f3l1xa88077/C2S/Report/Chapters/Intro/Milestones.tex

The project has been divided into five key-phases that each act as sub-projects and each lead into the next. This helps compartmentalise the project for better management and tracking.
\begin{table}[H]
\centering
\begin{tabular}{|l|p{12cm}|}
\hline
\textbf{ID} & \textbf{Milestone} \\
\hline
1 & Design and build a fully custom CubeSat-compatible prototype camera module, including PCB layout, component selection, and sensor integration. \\
\hline
2 & Develop firmware to configure and control the image sensor (e.g., via I\textsuperscript{2}C/SPI), supporting raw image capture and tuning of parameters like exposure, gain, and white balance. \\
\hline
3 & Implement an image pipeline to convert raw sensor data into usable image formats, including demosaicing, gamma correction, and compression. \\
\hline
4 & Design a mechanical housing that meets CubeSat volume, mass, and thermal constraints, and could interface with the rest of the CubeSat. \\
\hline
5 & Test and validate the camera module under simulated space conditions (thermal cycling, vibration, and low light). \\
\hline
\end{tabular}
\caption{Milestone objectives for the duration of the project}
\label{tab:milestones}
\end{table}
