f3l1xa88077/C2S/Report/Chapters/Pre/Summary.tex

This report is a long document, and it is easy to get lost in. The following text aims to help you navigate to the right sections depending on your need. Unfortunately, this project had generated a substantial amount of information, so some key considerations may have been missed or skipped. This report won't teach you everything I know, but \textbf{it will place you in my shoes and teach you why I made my decisions}.
\nl
\autoref{sec:intro} is your extended version of the project proposal. It explores a generic background and rationale for the project. Following this, the project scope is broken down and clearly explained, outlining exactly what is and isn't part of the project. Project milestones illustrate the core outcomes from the project and the responsibilities section shows how each milestone is divided between project members. Lastly, the project timeline presents the expected progression of the project.
\nl
Before diving into the other explanations, it's worth quickly understanding what I'll be referring to when I say v0, v0.1, and v1. It was intended that the project would include two versions, the first being a prototype to confirm functionality (v0), and a flight prototype (v1). Unfortunately, the test board needed to be redesigned, so a revised version of v0 was created, v0.1.
\nl
\autoref{sec:c2sv0} explores the first version of the project's (C2Sv0) hardware that used the MIPI CSI-2 camera interface, which was eventually shelved. This section critically explores each of the core system components and provides thorough justications for each selection. These components mainly map to those used in C2Sv0, but their considerations and justifications are still relevant. You may find that this version is often referred to as the \textit{"breakout board"} or \textit{"P, S, A"} meaning (P)rocessor, (S)ensor, and (A)daptor. The schematic and PCB designs were split into separate sections. This version was deprioritised because the only chips that support the CSI-2 interface have a BGA pitch too fine for manufacturing within current budget limitations. Although this board was not procured, many circuits were recycled for the succeeding version (v0.1) and the content is still worth a read, especially for the CSI-2 interface information.
\nl
\autoref{sec:c2sv0.1} investigates the second version of the project's (C2Sv0.1) hardware which supported the DCMI camera interface. Unlike v0, this interface is older, so the chips that support the interface have much larger packages which were within our manufacturing capabilities. Like v0, the schematics and PCBs are split into different sections. Errors and fixes are mentioned as a remark for each section. \autoref{sec:manufacturing-v0.1} outlines the processes involved in manufacturing and developing the hardware. This involes where the components where sourced from, how the components were placed, as well as the 3D printed designs. \autoref{sec:v0.1-coding} dives into programming the hardware from the previous section. It focuses on coding each individual subsystem first, then tests them all together to confirm compatability.
\nl
The Appendices (\autoref{sec:appendices}) are supplementary materials that are non-essential to the project, but are a useful read. For example, some of the research is included to fill in gaps of knowledge. To the average reader, this is not-critical, but can be insightful.
