f3l1xa88077/C2S/Report/Chapters/v1/Software/Software.tex

These goals were developed from my experiences of what had and hadn't worked with the previous versions, so they may not be perfect, but these are what I found to be the most important steps in camera development. Additionally, it makes writing and, in your case, reading, a lot easier to digest.

% -----------------------
% Setup
% -----------------------
\subsubsection{STM32CubeIDE Setup}

% -----------------------
% Isolated
% -----------------------
\subsubsection{Isolated Testing}

    \subsubsubsection{LEDs}
        \subimport{./Isolated/}{LEDs.tex}

    \subsubsubsection{Button}
        \subimport{./Isolated/}{Button.tex}

    \subsubsubsection{CSA}
        \subimport{./Isolated/}{CSA.tex}

    \subsubsubsection{QSPI}
        \subimport{./Isolated/}{QSPI.tex}

    \subsubsubsection{Sleep}
        \subimport{./Isolated/}{Sleep.tex}

    \subsubsubsection{RTOS}
        \subimport{./Isolated/}{RTOS.tex}

    \subsubsubsection{USB}
        \subimport{./Isolated/}{USB.tex}

    \subsubsubsection{Camera}
        \subimport{./Isolated/}{Camera.tex}

    \subsubsubsection{microSD}
        \subimport{./Isolated/}{microSD.tex}
