f3l1xa88077/C2S/Report/Chapters/Appendices/Supporting Calculations/Stitching.tex

For a given frequency, the center-to-center pitch between the vias should be less than approximately:
\begin{equation}
    L < \frac{c}{8f\sqrt{Dk}}
\end{equation}
