f3l1xa88077/C2S/Report/Chapters/Appendices/Supporting Calculations/Supporting Calculations.tex

\subsection{C-L-C Values}\label{sec:clc-values}
    \subimport{./}{CLC.tex}

% \subsection{Transconductance of Oscillator}
%     \subimport{./}{Transconductance.tex}

% \subsection{Power Draw Estimation}\label{sec:power-draw}
%     \subimport{./}{Power Estimation.tex}

\subsection{Stitching Via Calculations}\label{sec:stitching-calc}
    \subimport{./}{Stitching.tex}
