f3l1xa88077/C2S/Report/Chapters/v1/Planning/Trade.tex

A trade study is a structured evaluation used to identify the most balanced technical solution from a set of alternatives. This helps identify critical system indicators like interface standards and memory type that are vital for developing strong system requirements.

\subsubsubsection{CIS}
    \subimport{./Trade/}{Sensor.tex}

\subsubsubsection{OBC Interface}
    \subimport{./Trade/}{OBC.tex}

\subsubsubsection{CSA}\label{sec:v1-trade-csa}
    \subimport{./Trade/}{CSA.tex}

\subsubsubsection{Memory}\label{sec:v1-trade-memory}
    \subimport{./Trade/}{Memory.tex}

\subsubsubsection{MCU}
    \subimport{./Trade/}{MCU.tex}

\subsubsubsection{Power}
    \subimport{./Trade/}{Power.tex}
