f3l1xa88077/C2S/Report/Chapters/v1/Hardware/Schematic/Clocks.tex

I was able to recycle the same clocks from \autoref{sec:v0.1-clocks} since the x and the x had the same frequency requirements.

\begin{itemize}
    \item \href{https://www.mouser.com/ProductDetail/ECS/ECS-TXO-2016-33-400-TR?qs=PzGy0jfpSMtctR53CPxRHg%3D%3D}{40 MHz TCXO Oscillator (MCU)}
    \item \href{https://www.mouser.com/ProductDetail/ECS/ECS-327TXO-2012-33-TR?qs=amGC7iS6iy%252Bnhf6zW2Y7hQ%3D%3D}{32.768 kHz TCXO Oscillator (MCU)}
\end{itemize}

Since all three oscillators are TCXO, they already include internal circuitry (like the capacitor configuration) and simply need to be connected to the input pins of the STM32.
Each oscillator should continuously produce a clock signal when its tri-state function is enabled. The tri-state pins are tied to VDD so the clocks are always enabled, allowing the MCU to use HSE and LSE during sleep.
\nl
Future versions of the project could connect to the tri-state to the OBC CS line via a NOT gate, which allows the clocks to be externally controlled by the OBC, or continuously run. This switch would allow the OBC to place the clocks into low power mode, and keep the clocks always running during programming when power consumption is not an issue. Then the MCU could switch between its internal and external clocks between sleep modes to save power. This is a complicated approach and was not a requirement for the current verison, so it was not implemented.

\paragraph{Remark}
As the Real Time Clock (RTC) is not used, it was not necessary to include an LSE.
