f3l1xa88077/C2S/Report/Chapters/v1/Hardware/Schematic/Connectors.tex

Camera connector according to \autoref{sec:v1-schematic-sensor}.
\nl
As mentioned in \autoref{sec:v1-schematic-mcu}, a protective resistor was placed in series with the master selector header. OBC 16-pin FFC/FPC connector was reversed to ensure proper connection.
\nl
Please see \autoref{sec:v1-schematic-stlink} for more regarding the STLINK/V2 connector.
\nl
The microSD breakout header pinout developed according to the \href{https://core-electronics.com.au/attachments/localcontent/microSD-Breakout-v14_8139a6ca52.pdf}{BOB-00544 schematic}. Orientation did not matter since the header could be rotated 180° on the PCB.

\paragraph{Remark}
After the PCB was developed and manufactured, the 16-pin FPC pinout on OBC was reversed, so a reverse cable is required otherwise a short-circuit will occur.
\textbf{It is imperative that a reverse cable is used}.
