f3l1xa88077/C2S/Report/Chapters/v1/Software/Isolated/Button.tex

The button was configured as an external interrupt pin, triggering on the rising edge. Inside the interrupt file, the pin is checked and then sets a flag to capture an image.
