f3l1xa88077/C2S/Report/Chapters/v1/Software/Isolated/LEDs.tex

The LEDs were configured as GPIO outputs, driving HIGH to turn on the LEDs.
