f3l1xa88077/C2S/Report/Chapters/v1/Software/Isolated/microSD.tex

As outlined in \autoref{sec:v1-microSD}, the SPI interface was not configured correctly, so it was not possible to write/read to the microSD card. I did try adapting SPI libraries and bit-banging with a GPIO pin, but I had no luck.
