f3l1xa88077/C2S/Report/Chapters/v1/Software/Isolated/QSPI.tex

The QSPI driver was carried over from v0.1.
