f3l1xa88077/C2S/Report/Chapters/v1/Hardware/Schematic/Power.tex

The power circuit is responsible for sinking current and delivering stable voltages to the rest of the board. There are five clearly defined sections in the power delivery schematic.

\paragraph{1a. USB-C Connection}
A USB-C connector uses 5.1 k$\Omega$ pull down resistors (as outlined on page 54 of \cite{ti-usb-typec-guide}) to convert the load to a sink. The connector outputs +VUSB, which should be roughly 5V according to \cite{ti-usb-typec-guide}. The communication pins have been left as NC since the STLINK already provides a virtual COM port.

\paragraph{1b. EPS Connection}
Sinks a stable 5V from the EPS board, named +VEPS.

\paragraph{2. Source Selection}
A three pin header allows the power source to be selected by shorting the middle pin with either the USB or EPS voltage. The output is +VSEL (Voltage Selected).

\paragraph{3. Power Measurement}
+VSHUNT is passed through a shunt resistor, where the voltage difference is recorded by an INA219 CSA (as selected in \autoref{sec:v1-trade-csa}). 
With both address pins of the INA219 tied to ground, its address becomes 0x40, which does not clash with the read and write addresses of the OV7670 (0x42 and 0x43).
The CSA outputs current, voltage, and power data via I2C. The terminating side of the shunt resistor has +VCSA.
The selected LDO has a maximum output current of 300 mA on 3V3 logic which sinks 200 mA at 5V.
I selected the shunt resistor value according to the maximum voltage range (gain /8) of the INA219, this meant if less current was being drawn, the gain could be changed for increased accuracy i.e., worst case scenario the gain is /8 and I can characterise at max current draw, or during power-efficient modes where the current draw is low, I could change the range to $\pm$80 mV or $\pm$ 40 mV for better accuracy.
To achieve a 320 mV swing at 200 mA, a 1.6 $\Omega$ shunt resistor, the \href{https://au.mouser.com/ProductDetail/Panasonic/ERJ-6DQF1R6V?qs=WO7YBshssFHHp%2FMEk%2F2ARA%3D%3D}{ERJ-6DQF1R6V} was selected.
The 0805 package was selected to make the shunt more identifiable, although the 0603 package was perfectly fine to use.
The shunt resistor will dissipate some power, 64 mW at its peak, but we know its resistance and the current going through, so we can subtract its dissipated power from the total power to identify how much power only the board is consuming.

\paragraph{4. Filtering}
+VCSA is then passed through a pi-filter (CLC network) to reject any high-frequency noise, with output +VFILT (Voltage Filtered). I chose capacitor values of $C_1=$100 nF and $C_2=$10 $\mu$F (\autoref{sec:clc-values}) to create a cut-off frequency $\approx$1 MHz.

\paragraph{5. 3V3 Regulation}
Lastly, +VFILT is regulated to +3V3 using a Low-Dropout (LDO) regulator, specifically, the \href{https://au.mouser.com/ProductDetail/Texas-Instruments/TPS7A2033PDBVR?qs=hd1VzrDQEGjk%2FOBnRfKB4A%3D%3D}{TPS7A2033PDBVR}. This component was selected because of its high Power Supply Rejection Ratio (PSRR), its ability to provide a low-noise DC output for sensitive analog components, and its minimal PCB footprint due to the lack of an external inductor (see \autoref{sec:v1-sensor-power} for more about the specifics of PSRR). The datasheet was followed to populate the schematic.
