f3l1xa88077/C2S/Report/Chapters/v1/Hardware/PCB/Power Pad.tex

The same design considerations from version 0.1 were used, please see \autoref{sec:v0.1-powerpad} for more.
