f3l1xa88077/C2S/Report/Chapters/v1/Hardware/Schematic/Button.tex

Unlike for Version 0.1 in \autoref{sec:v0.1-sch-other}, only one button was used as the NRST pin was connected to the STLINK/V2 and BOOT0 could be left inactive according to \href{https://community.st.com/t5/stm32-mcus-boards-and-hardware/confused-over-correct-connections-for-boot0-nrst-and-swd/td-p/61611}{this article}. In addition, the \href{https://au.mouser.com/c/electromechanical/switches/tactile-switches/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}{PTS636} was used as it was the smallest and cheapest button that appeared in the Mouser search for tactile ON-OFF SMD/SMT switches. Keeping the button size small helped making space for more larger and more space-critical components like the connectors. The 2-pin symbol also made it impossible to short VCC and GND on the pinout.
