f3l1xa88077/C2S/Report/Chapters/v0/Intro/Introduction.tex

This phase focuses on establishing the foundation for the project by defining system requirements, selecting the image sensor, planning the preliminary architecture, and conducting initial parts research.
\nl
\textit{Please note. Although certain components are investigated, I only focus on key-components like the sensor and processor. Resistors, capacitors, debug LEDs and other components mentioned in dataSchematic (like recommended circuits) are not discussed. For more information, please see \autoref{sec:v0-schematic}}
