f3l1xa88077/C2S/Report/Chapters/v0/Schematic/Overview.tex

This phase involves designing the camera circuit schematic using Altium Designer, laying the groundwork for subsequent PCB development and component selection.
\nl
The schematic is divided into eight sub-sheets:
\begin{enumerate}[noitemsep]
    \item Processor
    \item Image Sensor
    \item Clocks
    \item uSD Card
    \item LPS
    \item SWD Connector
    \item USBC Connector
    \item Power Sequencer
\end{enumerate}
