f3l1xa88077/C2S/Report/Chapters/v0/Schematic/SWD.tex

The SWD connector followed the \href{https://www.youtube.com/watch?v=PMEpQZ90f34}{Phil's Lab guide} on STM32 PCB design, as well as referencing the ADCS Integration Board for the component.
