f3l1xa88077/C2S/Report/Chapters/v0/Schematic/uSD.tex

I used the getting started guide to construct the uSD Card schematic. Like the guide, I used the \href{https://au.mouser.com/ProductDetail/Nexperia/NXS0506GUX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}{NXS0506GUX} since the recommended component uses a BGA package that is too fine.
\nl
For faster readout speeds, I have connected the component in 4-bit mode, opposed to the simpler, but slower, 1-bit mode (connecting only DAT0).
\nl
Additionally, I added a decoupling capacitor to VCC using same value as the decoupling capacitors used on the image sensor.
