f3l1xa88077/C2S/Report/Chapters/v0.1/Programming/Isolated/Isolated.tex

\subsubsubsection{LEDs}
\subimport{./}{LEDs.tex}

\subsubsubsection{Audio Buzzer}\label{sec:buzzer}
\subimport{./}{Buzzer.tex}

\subsubsubsection{Rotary Encoder}
\subimport{./}{Encoder.tex}

\subsubsubsection{Current Sense Amplifier}\label{sec:csa}
\subimport{./}{CSA.tex}

\subsubsubsection{OR Gate}
\subimport{./}{OR.tex}

\subsubsubsection{Buttons}
\subimport{./}{Buttons.tex}

\subsubsubsection{QSPI}
\subimport{./}{QSPI.tex}

\subsubsubsection{microSD}
\subimport{./}{uSD.tex}

\subsubsubsection{Image Sensor}
\subimport{./}{Sensor.tex}
