f3l1xa88077/C2S/Report/Chapters/v0.1/Programming/Isolated/QSPI.tex

Because there were no publicly available drivers for the \href{https://www.renesas.com/en/products/at25sf2561c/part-details/at25sf2561c-mwub-t}{AT25SF2561C} QSPI memory, I developed a custom driver to interface with our hardware. While STM32CubeIDE provides the underlying HAL functions to support the QSPI interface, the driver logic had to be built from scratch by following the device \href{https://www.renesas.com/en/document/dst/at25sf2561cat25qf2561c-datasheet?r=25559121}{datasheet}.
\nl
The HAL functions operate on \verb|sCommand|, a struct that tells the HAL everything it needs to know like the address, the amount of bytes, how many lines the instruction will be sent on, etc. At its core, my driver simply grabs all the information it needs to, packages it into this \verb|sCommand| struct and feeds that to the HAL to handle the read/write.
Naturally the driver is more complex than this, but if you analyse the code, you will see lots of lines like \verb|QSPI_Memory->sCommand->...| which are just packing the data into the struct.
\nl
Now, by analysing the command set and register maps, I identified four primary operations required for the driver:
\begin{enumerate}[label=(\roman*)]
    \item Writing a byte to a specific configuration or status register.
    \item Reading a byte from a register to monitor device status.
    \item Sending standalone opcodes/commands for state control.
    \item Executing memory erase operations (sector or block level).
\end{enumerate}
Every other high-level function in the driver is essentially a combination of these four primitives.

Before the chip can handle standard read, write, or erase tasks, a specific initialisation sequence is required:
\begin{itemize}
    \item Setting the Write Enable Latch in Status Register (SR) 1.
    \item Validating the Ready/Busy bit in SR1 to ensure the chip isn't mid-operation.
    \item Enabling 4-line data transfer in SR2.
    \item Configuring latency in SR3 to match our clock frequency.
    \item Entering 4-byte address mode to access the full memory capacity beyond $16$\,MB.
\end{itemize}

A technical constraint of the hardware is that the standard write command is limited to a single $256$-byte page. To handle larger data writes, the driver segments the data into $256$-byte chunks and automatically increments the address pointer to the next page once the current one is full. This allows for contiguous data writing without manual page management.
\nl
Beyond the basic command set, several hardware-level constraints were addressed to ensure data integrity:
\begin{itemize}
    \item While the device supports 256-byte page programming, memory must be cleared in 4\,kB sectors before a rewrite can occur. The driver includes safety checks to prevent writing to non-erased blocks.
    \item The 4-byte address mode and dummy cycle configurations are volatile; the driver re-initialises these parameters on every power-on reset to ensure the memory map is consistently accessible.
    \item All polling loops for the RDY/BSY bit incorporate defined timeout periods to prevent CPU hang-ups in the event of hardware communication failure.
\end{itemize}

To simplify the integration of the driver into the flight software, I had created a \verb|DataBlock| structure to manage data transfers. This structure bundles the data size, source/destination pointers, and memory addresses into a single object, helping to abstract and simplify the code.
\nl
The driver's internal address management automatically updates its tracker. This ensures that subsequent write calls will append data to the next available 4\,kB-aligned sector, preventing data overwrites.
\nl
The driver utilises a LIFO (Last-In, First-Out) stack architecture for memory management, so new data chunks are pushed onto the next available address. Erase operations are designed to pop the most recent data by moving the address tracker backward. Because the address tracker is a single scalar value, erasure must occur in reverse-chronological order. Erasing a chunk at the start or middle of the memory would cause the tracker to point toward valid data further up the stack, leading to addressing conflicts.
\nl
Although the data chunks could be managed with a data structure, the symptoms of implementing a structure introduces far more complex problems than positive benefits. For example, two image chunks $I_1$ and $I_2$ with two characteristic sizes cannot be stored side by side without wastage. If $I_1$ is stored directly before $I_2$ in memory, then $I_1$ cannot be deleted and replaced with a chunk of different size without overwriting $I_2$ of leaving empty space between the chunks. For these reasons, implementing data structures is not within the current scope. Instead careful usage of the driver is urged.
