f3l1xa88077/C2S/Report/Chapters/v0.1/Programming/Isolated/uSD.tex

Since the U5 can do internal pull-ups on the data lines with ESD protection, the resistors could have been omitted from this version as mentioned by \href{https://www.youtube.com/watch?v=aEwwQMdKd-c\&t=248s}{Phil's Lab} \cite{phils-lab-sd}. Although, as mentioned in the video, it is recommended to include the resistors for the final build \cite{phils-lab-sd}.
\nl
FileX was used to write and read data to the microSD card. A stream data function was generated to allow larger files to be written, like image data.
