f3l1xa88077/C2S/Report/Chapters/v0.1/Hardware/PCB/Fiducial.tex

Fiducial markers were added to the sensor board (labelled "FM"). Three global markers were added near the corners of the board, and one local marker was added next to pin 1 of the BGA.
Although a pick and place machine is not used, it may help AT\&MWA when they attempt to place the BGA component.
\nl
Fiducial markers were also added to the corners of the processor PCB, although they will probably remain unused (no silkscreen label).
