f3l1xa88077/C2S/Report/Chapters/v0.1/Hardware/PCB/Power Pad.tex

For thermal management on the QSPI memory chip, I used vias of 0.6/0.3mm diameter spaced at 1mm to provide thermal relief to the component (see \autoref{fig:power-pad}) \cite{TI-SLOA120}.
\begin{figure}
    \centering
    
    \caption{Power pad used on QSPI memory chip.}
    \label{fig:power-pad}
\end{figure}
