f3l1xa88077/C2S/Report/Chapters/v0.1/Programming/CubeIDE/CubeIDE.tex

Start the project by either downloading the complete project file from the \href{https://github.com/PerthAerospaceStudentTeam/C2S/tree/main/Software/v0.1}{GitHub Repository}, or create a new project with the STM32U5G9ZJTX6Q processor.

\paragraph{RCC}
\subimport{./}{RCC.tex}

\paragraph{SYS}
\subimport{./}{SYS.tex}

\paragraph{ADC1}
\subimport{./}{ADC1.tex}

\paragraph{TIM1}
\subimport{./}{TIM1.tex}

\paragraph{I2C}
\subimport{./}{I2C.tex}

\paragraph{OSPI}
\subimport{./}{OSPI.tex}

\paragraph{SDMMC1}
\subimport{./}{SDMMC1.tex}

\paragraph{SPI1}
\subimport{./}{SPI1.tex}

\paragraph{USART}
\subimport{./}{USART.tex}

\paragraph{DCMI}
\subimport{./}{DCMI.tex}

\paragraph{JPEG}
\subimport{./}{JPEG.tex}

\paragraph{FILEX}
\subimport{./}{FILEX.tex}

\paragraph{DEBUG}
\subimport{./}{DEBUG.tex}

\paragraph{GPDMA1}
\subimport{./}{GPDMA1.tex}

\paragraph{GPIO}
\subimport{./}{GPIO.tex}
