f3l1xa88077/C2S/Report/Chapters/v0.1/Programming/CubeIDE/I2C.tex

Three I2C interfaces are included, with one dedicated to communicating with the image sensor, another to write to the LCD screen, and the other as a general peripheral.
I2C1, I2C2, and I2C4 should all be enabled and should appear on pins 128 \& 129, 10 \& 11, and 62 \& 63, respectively.
