f3l1xa88077/C2S/Report/Chapters/v0.1/Programming/CubeIDE/SPI1.tex

The SPI interface is a non-critical peripheral that can be used for any purpose you like. Make sure to enable SPI1 by changing to 'Transmit Only Master'.
