f3l1xa88077/C2S/Report/Chapters/v0.1/Programming/CubeIDE/USART.tex

The USART interfaces are non-critical and can be used for interacting with the board.
Enable USART1 and USART2 in 'Synchronous Master' mode, they should populate on pins 102-104 and 38, 39 \& 124, respectively.
