f3l1xa88077/C2S/Report/Chapters/v0.1/Programming/Isolated/Buttons.tex

Using the STM32CubeIDE, I set each button's pin to be an interrupt and enabled the interrupt in the NVIC tab. I then used a basic software debounce.
