f3l1xa88077/C2S/Report/Chapters/v0.1/Programming/Isolated/OR.tex

As explored in \autoref{sec:v0-sch-other}, the OR gate was not functional so the pins associated with the circuit were assigned in the STM32CubeIDE, but were not used.
