f3l1xa88077/C2S/Report/Chapters/v0/Requirements/Components/Clock.tex

The \href{https://au.mouser.com/ProductDetail/ECS/ECS-TXO-3225MV-240-TR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}{ECS-TXO-3225MV-240-TR} was selected primarily because it provides a highly stable and precise 24 MHz clock signal, which perfectly suits our system's timing requirements.
This temperature-compensated crystal oscillator (TCXO) ensures minimal frequency drift across varying thermal conditions, a critical factor for reliable operation in aerospace environments.
Additionally, the Avionics Department Representative recommended a TXCO, reinforcing its suitability for our application. Since the design only requires a single clock output rather than a differential pair, this oscillator meets our needs efficiently without unnecessary complexity.
Additionally, the MIRA220 image sensor also requires a 24MHz reference clock, so only a single external clock is required for the breakout. Although the clock is connected to two components, its load capacitance of 15pF should prevent any overloading symptoms.
