f3l1xa88077/C2S/Report/Chapters/v0/Requirements/Components/LPS.tex

Opposed to a switching converter, an LDO was chosen because of the cost and fewer external components required.
Since the required power lines will most likely come from other projects like EPS, LDOs were a great choice for cheap and compact local power supplies on the breakout board.
\nl
The \href{https://au.mouser.com/c/semiconductors/power-management-ics/voltage-regulators-voltage-controllers/ldo-voltage-regulators/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}{TCR3DF} series Linear Drop-Off Voltage Regulators (LDOs) were selected as the local power supplies for the breakout board because I could source all of the required power lines from the same series.
An extensive search for LDOs was not conducted since the first results met the criteria and I did not see a need to further optimise the component selection.
