f3l1xa88077/C2S/Report/Chapters/v0.1/Manufacturing/3D.tex

The \href{https://www.jaycar.com.au/green-push-on-style-knob/p/HK7711}{knob} I had that was meant to be used on the rotary encoder did not fit, so, I 3D modelled one in Fusion360.
I added some grip so it would be easier to rotate by following \href{https://www.youtube.com/watch?v=i3aDl9bQ-oY}{this YouTube guide}.

\begin{indentedfigure}
    \centering
    \begin{subfigure}[b]{0.3\textwidth}
        \centering
        
        \caption{Top-down view}
    \end{subfigure}
    \hspace{2cm}
    \begin{subfigure}[b]{0.3\textwidth}
        \centering
        
        \caption{Bottom-up view}
    \end{subfigure}
    \caption{Knob modelled in Fusion360}
\end{indentedfigure}

Additionally, a supporting stub was required for the new shield PCB. This was a simple matter of measuring how high the PCB would sit and recording the diameter of the mounting holes. Both 3D models can be found in the GitHub repo \href{https://github.com/f3l1xa88077/C2S/tree/main/Hardware/v0.1/3D%20Prints}{here}.
