f3l1xa88077/C2S/Testing/C2Sv1/VGA_RGB565/power_log_2026-08-02_16-11-55.csv

Timestamp | Event Type | Power (mW) | Notes
2026-08-02T08:11:44.810Z | IMAGE_REQUESTED |  | Res: VGA, Mode: RGB565
2026-08-02T08:11:44.811Z | POWER_SAMPLE | 149
2026-08-02T08:11:44.880Z | POWER_SAMPLE | 217
2026-08-02T08:11:44.950Z | POWER_SAMPLE | 218
2026-08-02T08:11:45.020Z | POWER_SAMPLE | 221
2026-08-02T08:11:45.090Z | POWER_SAMPLE | 222
2026-08-02T08:11:45.160Z | POWER_SAMPLE | 220
2026-08-02T08:11:45.230Z | POWER_SAMPLE | 225
2026-08-02T08:11:45.300Z | POWER_SAMPLE | 223
2026-08-02T08:11:45.370Z | POWER_SAMPLE | 218
2026-08-02T08:11:45.440Z | POWER_SAMPLE | 219
2026-08-02T08:11:45.510Z | POWER_SAMPLE | 218
2026-08-02T08:11:45.580Z | POWER_SAMPLE | 218
2026-08-02T08:11:45.650Z | POWER_SAMPLE | 219
2026-08-02T08:11:45.720Z | POWER_SAMPLE | 219
2026-08-02T08:11:45.790Z | POWER_SAMPLE | 218
2026-08-02T08:11:45.860Z | POWER_SAMPLE | 224
2026-08-02T08:11:45.930Z | POWER_SAMPLE | 223
2026-08-02T08:11:46.000Z | POWER_SAMPLE | 219
2026-08-02T08:11:46.070Z | POWER_SAMPLE | 220
2026-08-02T08:11:46.140Z | POWER_SAMPLE | 218
2026-08-02T08:11:46.210Z | POWER_SAMPLE | 218
2026-08-02T08:11:46.280Z | POWER_SAMPLE | 218
2026-08-02T08:11:46.350Z | POWER_SAMPLE | 218
2026-08-02T08:11:46.420Z | POWER_SAMPLE | 260
2026-08-02T08:11:46.490Z | POWER_SAMPLE | 261
2026-08-02T08:11:46.560Z | POWER_SAMPLE | 259
2026-08-02T08:11:46.630Z | POWER_SAMPLE | 222
2026-08-02T08:11:46.700Z | POWER_SAMPLE | 246
2026-08-02T08:11:46.770Z | POWER_SAMPLE | 228
2026-08-02T08:11:46.840Z | POWER_SAMPLE | 219
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
2026-08-02T08:11:52.253Z | POWER_SAMPLE | 158
2026-08-02T08:11:52.316Z | POWER_SAMPLE | 151
2026-08-02T08:11:52.396Z | POWER_SAMPLE | 151
2026-08-02T08:11:52.460Z | POWER_SAMPLE | 155
2026-08-02T08:11:52.538Z | POWER_SAMPLE | 153
2026-08-02T08:11:52.597Z | IMAGE_RENDERED |  | 640x480
