f3l1xa88077/C2S/Testing/C2Sv1/VGA_RGB565/power_log_2026-08-02_16-12-36.csv

Timestamp | Event Type | Power (mW) | Notes
2026-08-02T08:12:25.891Z | IMAGE_REQUESTED |  | Res: VGA, Mode: RGB565
2026-08-02T08:12:25.905Z | POWER_SAMPLE | 149
2026-08-02T08:12:25.975Z | POWER_SAMPLE | 220
2026-08-02T08:12:26.045Z | POWER_SAMPLE | 217
2026-08-02T08:12:26.115Z | POWER_SAMPLE | 219
2026-08-02T08:12:26.185Z | POWER_SAMPLE | 222
2026-08-02T08:12:26.255Z | POWER_SAMPLE | 222
2026-08-02T08:12:26.325Z | POWER_SAMPLE | 225
2026-08-02T08:12:26.395Z | POWER_SAMPLE | 225
2026-08-02T08:12:26.465Z | POWER_SAMPLE | 219
2026-08-02T08:12:26.535Z | POWER_SAMPLE | 217
2026-08-02T08:12:26.605Z | POWER_SAMPLE | 222
2026-08-02T08:12:26.675Z | POWER_SAMPLE | 218
2026-08-02T08:12:26.745Z | POWER_SAMPLE | 216
2026-08-02T08:12:26.815Z | POWER_SAMPLE | 220
2026-08-02T08:12:26.885Z | POWER_SAMPLE | 218
2026-08-02T08:12:26.955Z | POWER_SAMPLE | 224
2026-08-02T08:12:27.025Z | POWER_SAMPLE | 225
2026-08-02T08:12:27.095Z | POWER_SAMPLE | 218
2026-08-02T08:12:27.165Z | POWER_SAMPLE | 217
2026-08-02T08:12:27.235Z | POWER_SAMPLE | 222
2026-08-02T08:12:27.305Z | POWER_SAMPLE | 219
2026-08-02T08:12:27.375Z | POWER_SAMPLE | 218
2026-08-02T08:12:27.445Z | POWER_SAMPLE | 220
2026-08-02T08:12:27.515Z | POWER_SAMPLE | 223
2026-08-02T08:12:27.585Z | POWER_SAMPLE | 262
2026-08-02T08:12:27.655Z | POWER_SAMPLE | 222
2026-08-02T08:12:27.725Z | POWER_SAMPLE | 223
2026-08-02T08:12:27.795Z | POWER_SAMPLE | 254
2026-08-02T08:12:27.865Z | POWER_SAMPLE | 232
2026-08-02T08:12:27.935Z | POWER_SAMPLE | 222
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
2026-08-02T08:12:33.348Z | POWER_SAMPLE | 153
2026-08-02T08:12:33.427Z | POWER_SAMPLE | 155
2026-08-02T08:12:33.490Z | POWER_SAMPLE | 151
2026-08-02T08:12:33.554Z | POWER_SAMPLE | 154
2026-08-02T08:12:33.632Z | POWER_SAMPLE | 157
2026-08-02T08:12:33.693Z | IMAGE_RENDERED |  | 640x480
