f3l1xa88077/C2S/Report/Chapters/v0.1/Programming/CubeIDE/DEBUG.tex

The DEBUG mode should be set to Serial Wire. SWCLK and SWDIO DEBUG should populate on pins 111 and 107, respectively.
