f3l1xa88077/C2S/Software/C2Sv1/Drivers/Custom/tinyusb/tusb_config.h

/*
 * The MIT License (MIT)
 *
 * Copyright (c) 2019 Ha Thach (tinyusb.org)
 *
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
 */

#ifndef TUSB_CONFIG_H_
#define TUSB_CONFIG_H_

#ifdef __cplusplus
 extern "C" {
#endif

//--------------------------------------------------------------------+
// Board Specific Configuration
//--------------------------------------------------------------------+

// RHPort number used for device can be defined by board.mk, default to port 0
#ifndef BOARD_TUD_RHPORT
#define BOARD_TUD_RHPORT      0
#endif

// RHPort max operational speed can defined by board.mk
#ifndef BOARD_TUD_MAX_SPEED
#define BOARD_TUD_MAX_SPEED   OPT_MODE_DEFAULT_SPEED
#endif

//--------------------------------------------------------------------
// Common Configuration
//--------------------------------------------------------------------

// defined by compiler flags for flexibility
#ifndef CFG_TUSB_MCU
#define CFG_TUSB_MCU OPT_MCU_STM32U5
#endif

#ifndef CFG_TUSB_OS
#define CFG_TUSB_OS           OPT_OS_THREADX
#endif

#ifndef CFG_TUSB_DEBUG
#define CFG_TUSB_DEBUG        0
#endif

// Enable Device stack
#define CFG_TUD_ENABLED       1

// Default is max speed that hardware controller could support with on-chip PHY
#define CFG_TUD_MAX_SPEED     BOARD_TUD_MAX_SPEED

/* USB DMA on some MCUs can only access a specific SRAM region with restriction on alignment.
 * Tinyusb use follows macros to declare transferring memory so that they can be put
 * into those specific section.
 * e.g
 * - CFG_TUSB_MEM SECTION : __attribute__ (( section(".usb_ram") ))
 * - CFG_TUSB_MEM_ALIGN   : __attribute__ ((aligned(4)))
 */
#ifndef CFG_TUSB_MEM_SECTION
#define CFG_TUSB_MEM_SECTION
#endif

#ifndef CFG_TUSB_MEM_ALIGN
#define CFG_TUSB_MEM_ALIGN    __attribute__ ((aligned(4)))
#endif

//--------------------------------------------------------------------
// DEVICE CONFIGURATION
//--------------------------------------------------------------------

// Synopsys DWC2 FIFO sizing allocation (in 32-bit words)
#define CFG_TUD_DWC2_BYTES_EP0      64

// TX FIFOs for Endpoints (Endpoint 0, CDC Notify, CDC Data)
#define CFG_TUD_DWC2_TX_FIFO_SIZES  { 16, 16, 256 } // Upgrade from FIFO size of 64 to 256

// RX FIFO size (Shared by all OUT endpoints)
#define CFG_TUD_DWC2_RX_FIFO_SIZE   128

#ifndef CFG_TUD_ENDPOINT0_SIZE
#define CFG_TUD_ENDPOINT0_SIZE   64
#endif

//------------- CLASS -------------//
#define CFG_TUD_CDC              1
#define CFG_TUD_MSC              0
#define CFG_TUD_HID              0
#define CFG_TUD_MIDI             0
#define CFG_TUD_VENDOR           0

#define CFG_TUD_CDC_NOTIFY        1 // Enable use of notification endpoint

// CDC FIFO size of TX and RX
#define CFG_TUD_CDC_RX_BUFSIZE   512 // (TUD_OPT_HIGH_SPEED ? 512 : 64)
#define CFG_TUD_CDC_TX_BUFSIZE   4096 // (TUD_OPT_HIGH_SPEED ? 512 : 64)

// CDC Endpoint transfer buffer size, default to max bulk packet size (HS 512, FS 64). Larger is faster.
// Larger RX_EPSIZE requires CFG_TUD_CDC_RX_NEED_ZLP = 1 and host ZLP support
#define CFG_TUD_CDC_RX_EPSIZE  (TUD_OPT_HIGH_SPEED ? 512 : 64)
#define CFG_TUD_CDC_TX_EPSIZE  (TUD_OPT_HIGH_SPEED ? 512 : 64)

// MSC Buffer size of Device Mass storage
#define CFG_TUD_MSC_EP_BUFSIZE   512

//// Enable the Synopsys core's internal hardware DMA
//#define CFG_TUD_DWC2_DMA_ENABLE    1
//
//// Explicitly disable slave mode since DMA is handling memory transfers
//#define CFG_TUD_DWC2_SLAVE_ENABLE  0

#ifdef __cplusplus
 }
#endif

#endif /* TUSB_CONFIG_H_ */
