f3l1xa88077/C2S/Software/C2Sv1/Drivers/Custom/tinyusb/common/tusb_fifo.h

/*
 * The MIT License (MIT)
 *
 * Copyright (c) 2019 Ha Thach (tinyusb.org)
 * Copyright (c) 2020 Reinhard Panhuber - rework to unmasked pointers
 *
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
 * This file is part of the TinyUSB stack.
 */

#ifndef TUSB_FIFO_H_
#define TUSB_FIFO_H_

#ifdef __cplusplus
extern "C" {
#endif

#include <tinyusb/common/tusb_common.h>
#include <tinyusb/osal/osal.h>

//--------------------------------------------------------------------+
// Configuration
//--------------------------------------------------------------------+
// mutex is only needed for RTOS. For OS None, we don't get preempted
#define CFG_FIFO_MUTEX      OSAL_MUTEX_REQUIRED

#define CFG_TUSB_FIFO_HWFIFO_API (CFG_TUD_EDPT_DEDICATED_HWFIFO || CFG_TUH_EDPT_DEDICATED_HWFIFO)

#ifndef CFG_TUSB_FIFO_HWFIFO_DATA_STRIDE
  #define CFG_TUSB_FIFO_HWFIFO_DATA_STRIDE 0
#endif

#ifndef CFG_TUSB_FIFO_HWFIFO_ADDR_STRIDE
  #define CFG_TUSB_FIFO_HWFIFO_ADDR_STRIDE 0
#endif

// Due to the use of unmasked pointers, this FIFO does not suffer from losing
// one item slice. Furthermore, write and read operations are completely
// decoupled as write and read functions do not modify a common state. Henceforth,
// writing or reading from the FIFO within an ISR is safe as long as no other
// process (thread or ISR) interferes.
// Also, this FIFO is ready to be used in combination with a DMA as the write and
// read pointers can be updated from within a DMA ISR. Overflows are detectable
// within a certain number (see tu_fifo_overflow()).

/* Write/Read "pointer" is in the range of: 0 .. depth - 1, and is used to get the fifo data.
 * Write/Read "index" is always in the range of: 0 .. 2*depth-1
 *
 * The extra window allow us to determine the fifo state of empty or full with only 2 indices
 * Following are examples with depth = 3
 *
 * - empty: W = R
 *                |
 *    -------------------------
 *    | 0 | RW| 2 | 3 | 4 | 5 |
 *
 * - full 1: W > R
 *                |
 *    -------------------------
 *    | 0 | R | 2 | 3 | W | 5 |
 *
 * - full 2: W < R
 *                |
 *    -------------------------
 *    | 0 | 1 | W | 3 | 4 | R |
 *
 * - Number of items in the fifo can be determined in either cases:
 *    - case W >= R: Count = W - R
 *    - case W <  R: Count = 2*depth - (R - W)
 *
 * In non-overwritable mode, computed Count (in above 2 cases) is at most equal to depth.
 * However, in over-writable mode, write index can be repeatedly increased and count can be
 * temporarily larger than depth (overflowed condition) e.g
 *
 *  - Overflowed 1: write(3), write(1)
 *    In this case we will adjust Read index when read()/peek() is called so that count = depth.
 *                  |
 *      -------------------------
 *      | R | 1 | 2 | 3 | W | 5 |
 *
 *  - Double Overflowed i.e index is out of allowed range [0,2*depth)
 *    This occurs when we continue to write after 1st overflowed to 2nd overflowed. e.g:
 *      write(3), write(1), write(2)
 *    This must be prevented since it will cause unrecoverable state, in above example
 *    if not handled the fifo will be empty instead of continue-to-be full. Since we must not modify
 *    read index in write() function, which cause race condition. We will re-position write index so that
 *    after data is written it is a full fifo i.e W = depth - R
 *
 *      re-position W = 1 before write(2)
 *      Note: we should also move data from mem[3] to read index as well, but deliberately skipped here
 *      since it is an expensive operation !!!
 *                  |
 *      -------------------------
 *      | R | W | 2 | 3 | 4 | 5 |
 *
 *      perform write(2), result is still a full fifo.
 *
 *                  |
 *      -------------------------
 *      | R | 1 | 2 | W | 4 | 5 |
 */
typedef struct {
  uint8_t *buffer;              // buffer pointer
  uint16_t depth;               // max items
  bool     overwritable;        // overwritable when full
  // 1 byte padding here

  volatile uint16_t wr_idx;     // write index
  volatile uint16_t rd_idx;     // read index

#if OSAL_MUTEX_REQUIRED
  osal_mutex_t mutex_wr;
  osal_mutex_t mutex_rd;
#endif
} tu_fifo_t;

typedef struct {
  struct {
    uint16_t len; // length
    uint8_t *ptr; // buffer pointer
  } linear, wrapped;
} tu_fifo_buffer_info_t;

// Access mode for hardware fifo read/write
typedef struct {
  uint8_t   data_stride;
  uintptr_t param;
} tu_hwfifo_access_t;

#define TU_FIFO_INIT(_buffer, _depth, _overwritable) \
  {                                                  \
    .buffer       = _buffer,                         \
    .depth        = _depth,                          \
    .overwritable = _overwritable,                   \
  }

#define TU_FIFO_DEF(_name, _depth, _overwritable)                    \
  uint8_t   _name##_buf[_depth];                                     \
  tu_fifo_t _name = TU_FIFO_INIT(_name##_buf, _depth, _overwritable)

// Moving data from tusb_fifo <-> USB hardware FIFOs e.g. STM32s need to use a special stride mode which reads/writes
// data in 2/4 byte chunks from/to a fixed address (USB FIFO register) instead of incrementing the address. For this use
// read/write access_mode with stride_mode = true. The STRIDE DATA and ADDR stride must be configured with
// CFG_TUSB_FIFO_HWFIFO_DATA_STRIDE and CFG_TUSB_FIFO_HWFIFO_ADDR_STRIDE

//--------------------------------------------------------------------+
// Setup API
//--------------------------------------------------------------------+
bool tu_fifo_config(tu_fifo_t *f, void *buffer, uint16_t depth, bool overwritable);
void tu_fifo_set_overwritable(tu_fifo_t *f, bool overwritable);
void tu_fifo_clear(tu_fifo_t *f);

#if OSAL_MUTEX_REQUIRED
TU_ATTR_ALWAYS_INLINE static inline
void tu_fifo_config_mutex(tu_fifo_t *f, osal_mutex_t wr_mutex, osal_mutex_t rd_mutex) {
  f->mutex_wr = wr_mutex;
  f->mutex_rd = rd_mutex;
}
#else
#define tu_fifo_config_mutex(_f, _wr_mutex, _rd_mutex)
#endif

//--------------------------------------------------------------------+
// Index API
//--------------------------------------------------------------------+
void tu_fifo_correct_read_pointer(tu_fifo_t *f);

// Pointer modifications intended to be used in combinations with DMAs.
// USE WITH CARE - NO SAFETY CHECKS CONDUCTED HERE! NOT MUTEX PROTECTED!
void tu_fifo_advance_write_pointer(tu_fifo_t *f, uint16_t n);
void tu_fifo_advance_read_pointer(tu_fifo_t *f, uint16_t n);

// If you want to read/write from/to the FIFO by use of a DMA, you may need to conduct two copies
// to handle a possible wrapping part. These functions deliver a pointer to start
// reading/writing from/to and a valid linear length along which no wrap occurs.
void tu_fifo_get_read_info(tu_fifo_t *f, tu_fifo_buffer_info_t *info);
void tu_fifo_get_write_info(tu_fifo_t *f, tu_fifo_buffer_info_t *info);

//--------------------------------------------------------------------+
// Peek API
// peek() will correct/re-index read pointer in case of an overflowed fifo to form a full fifo
//--------------------------------------------------------------------+
uint16_t tu_fifo_peek_n_access_mode(tu_fifo_t *f, void *p_buffer, uint16_t n, uint16_t wr_idx, uint16_t rd_idx,
                                    const tu_hwfifo_access_t *access_mode);
bool     tu_fifo_peek(tu_fifo_t *f, void *p_buffer);
uint16_t tu_fifo_peek_n(tu_fifo_t *f, void *p_buffer, uint16_t n);

//--------------------------------------------------------------------+
// Read API
// peek() + advance read index
//--------------------------------------------------------------------+
uint16_t tu_fifo_read_n_access_mode(tu_fifo_t *f, void *buffer, uint16_t n, const tu_hwfifo_access_t *access_mode);
bool     tu_fifo_read(tu_fifo_t *f, void *buffer);
TU_ATTR_ALWAYS_INLINE static inline uint16_t tu_fifo_read_n(tu_fifo_t *f, void *buffer, uint16_t n) {
  return tu_fifo_read_n_access_mode(f, buffer, n, NULL);
}

// discard first n items from fifo i.e advance read pointer by n with mutex
// return number of discarded items
uint16_t tu_fifo_discard_n(tu_fifo_t *f, uint16_t n);

//--------------------------------------------------------------------+
// Write API
//--------------------------------------------------------------------+
uint16_t tu_fifo_write_n_access_mode(tu_fifo_t *f, const void *data, uint16_t n, const tu_hwfifo_access_t *access_mode);
bool     tu_fifo_write(tu_fifo_t *f, const void *data);
TU_ATTR_ALWAYS_INLINE static inline uint16_t tu_fifo_write_n(tu_fifo_t *f, const void *data, uint16_t n) {
  return tu_fifo_write_n_access_mode(f, data, n, NULL);
}

//--------------------------------------------------------------------+
// Hardware FIFO API
// Special hardware FIFO/Buffer to hold USB data, usually requires certain access method these can be configured with
// CFG_TUSB_FIFO_HWFIFO_DATA_STRIDE (data width) and CFG_TUSB_FIFO_HWFIFO_ADDR_STRIDE (address increment)
// Note: these usually has opposite direction (read/write) to/from our software FIFO  (tu_fifo_t)
//--------------------------------------------------------------------+
TU_ATTR_ALWAYS_INLINE static inline uint16_t tu_hwfifo_write_from_fifo(volatile void *hwfifo, tu_fifo_t *f, uint16_t n,
                                                                       const tu_hwfifo_access_t *access_mode) {
  const tu_hwfifo_access_t default_access = {.data_stride = CFG_TUSB_FIFO_HWFIFO_DATA_STRIDE, .param = 0};
  return tu_fifo_read_n_access_mode(f, (void *)(uintptr_t)hwfifo, n,
                                    (access_mode != NULL) ? access_mode : &default_access);
}

TU_ATTR_ALWAYS_INLINE static inline uint16_t tu_hwfifo_read_to_fifo(const volatile void *hwfifo, tu_fifo_t *f,
                                                                    uint16_t n, const tu_hwfifo_access_t *access_mode) {
  const tu_hwfifo_access_t default_access = {.data_stride = CFG_TUSB_FIFO_HWFIFO_DATA_STRIDE, .param = 0};
  return tu_fifo_write_n_access_mode(f, (const void *)(uintptr_t)hwfifo, n,
                                     (access_mode != NULL) ? access_mode : &default_access);
}

#if CFG_TUSB_FIFO_HWFIFO_API
// read from hwfifo to buffer
void tu_hwfifo_read(const volatile void *hwfifo, uint8_t *dest, uint16_t len, const tu_hwfifo_access_t *access_mode);

// write to hwfifo from buffer with access mode
void tu_hwfifo_write(volatile void *hwfifo, const uint8_t *src, uint16_t len, const tu_hwfifo_access_t *access_mode);

#endif

//--------------------------------------------------------------------+
// Internal Helper Local
// work on local copies of read/write indices in order to only access them once for re-entrancy
//--------------------------------------------------------------------+
// return overflowable count (index difference), which can be used to determine both fifo count and an overflow state
TU_ATTR_ALWAYS_INLINE static inline uint16_t tu_ff_overflow_count(uint16_t depth, uint16_t wr_idx, uint16_t rd_idx) {
  const int32_t diff = (int32_t)wr_idx - (int32_t)rd_idx;
  if (diff >= 0) {
    return (uint16_t)diff;
  } else {
    return (uint16_t)(2 * depth + diff);
  }
}

// return remaining slot in fifo
TU_ATTR_ALWAYS_INLINE static inline uint16_t tu_ff_remaining_local(uint16_t depth, uint16_t wr_idx, uint16_t rd_idx) {
  const uint16_t ovf_count = tu_ff_overflow_count(depth, wr_idx, rd_idx);
  return (depth > ovf_count) ? (depth - ovf_count) : 0;
}

//--------------------------------------------------------------------+
// State API
// Following functions are reentrant since they only access read/write indices once, therefore can be used in thread and
// ISRs context without the need of mutexes
//--------------------------------------------------------------------+
TU_ATTR_ALWAYS_INLINE static inline uint16_t tu_fifo_depth(const tu_fifo_t *f) {
  return f->depth;
}

TU_ATTR_ALWAYS_INLINE static inline bool tu_fifo_empty(const tu_fifo_t *f) {
  const uint16_t wr_idx = f->wr_idx;
  const uint16_t rd_idx = f->rd_idx;
  return wr_idx == rd_idx;
}

// return number of items in fifo, capped to fifo's depth
TU_ATTR_ALWAYS_INLINE static inline uint16_t tu_fifo_count(const tu_fifo_t *f) {
  const uint16_t wr_idx = f->wr_idx;
  const uint16_t rd_idx = f->rd_idx;
  return tu_min16(tu_ff_overflow_count(f->depth, wr_idx, rd_idx), f->depth);
}

// check if fifo is full
TU_ATTR_ALWAYS_INLINE static inline bool tu_fifo_full(const tu_fifo_t *f) {
  const uint16_t wr_idx = f->wr_idx;
  const uint16_t rd_idx = f->rd_idx;
  return tu_ff_overflow_count(f->depth, wr_idx, rd_idx) >= f->depth;
}

TU_ATTR_ALWAYS_INLINE static inline uint16_t tu_fifo_remaining(const tu_fifo_t *f) {
  const uint16_t wr_idx = f->wr_idx;
  const uint16_t rd_idx = f->rd_idx;
  return tu_ff_remaining_local(f->depth, wr_idx, rd_idx);
}

#ifdef __cplusplus
}
#endif

#endif
