f3l1xa88077/C2S/Software/C2Sv1/Drivers/Custom/tinyusb/device/dcd.h

/*
 * The MIT License (MIT)
 *
 * Copyright (c) 2019 Ha Thach (tinyusb.org)
 *
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
 * This file is part of the TinyUSB stack.
 */

#ifndef TUSB_DCD_H_
#define TUSB_DCD_H_

#include <tinyusb/common/tusb_common.h>
#include <tinyusb/common/tusb_fifo.h>
#include <tinyusb/osal/osal.h>

#ifdef __cplusplus
 extern "C" {
#endif

//--------------------------------------------------------------------+
// MACRO CONSTANT TYPEDEF PROTYPES
//--------------------------------------------------------------------+

typedef enum {
  DCD_EVENT_INVALID = 0,    // 0
  DCD_EVENT_BUS_RESET,      // 1
  DCD_EVENT_UNPLUGGED,      // 2
  DCD_EVENT_SOF,            // 3
  DCD_EVENT_SUSPEND,        // 4 TODO LPM Sleep L1 support
  DCD_EVENT_RESUME,         // 5
  DCD_EVENT_SETUP_RECEIVED, // 6
  DCD_EVENT_XFER_COMPLETE,  // 7
  USBD_EVENT_FUNC_CALL,     // 8 Not an DCD event, just a convenient way to defer ISR function
  DCD_EVENT_COUNT
} dcd_eventid_t;

typedef struct TU_ATTR_ALIGNED(4) {
  uint8_t rhport;
  uint8_t event_id;

  union {
    // BUS RESET
    struct {
      tusb_speed_t speed;
    } bus_reset;

    // SOF
    struct {
      uint32_t frame_count;
    }sof;

    // SETUP_RECEIVED
    tusb_control_request_t setup_received;

    // XFER_COMPLETE
    struct {
      uint8_t  ep_addr;
      uint8_t  result;
      uint32_t len;
    }xfer_complete;

    // FUNC_CALL
    struct {
      void (*func) (void* param);
      void* param;
    }func_call;
  };
} dcd_event_t;

//TU_VERIFY_STATIC(sizeof(dcd_event_t) <= 12, "size is not correct");

//--------------------------------------------------------------------+
// Memory API
//--------------------------------------------------------------------+

// clean/flush data cache: write cache -> memory.
// Required before an DMA TX transfer to make sure data is in memory
bool dcd_dcache_clean(const void* addr, uint32_t data_size);

// invalidate data cache: mark cache as invalid, next read will read from memory
// Required BOTH before and after an DMA RX transfer
bool dcd_dcache_invalidate(const void* addr, uint32_t data_size);

// clean and invalidate data cache
// Required before an DMA transfer where memory is both read/write by DMA
bool dcd_dcache_clean_invalidate(const void* addr, uint32_t data_size);

//--------------------------------------------------------------------+
// Controller API
//--------------------------------------------------------------------+

// optional dcd configuration, called by tud_configure()
bool dcd_configure(uint8_t rhport, uint32_t cfg_id, const void* cfg_param);

// Initialize controller to device mode
bool dcd_init(uint8_t rhport, const tusb_rhport_init_t* rh_init);

// Deinitialize controller, unset device mode.
bool dcd_deinit(uint8_t rhport);

// Interrupt Handler
void dcd_int_handler(uint8_t rhport);

// Enable device interrupt
void dcd_int_enable (uint8_t rhport);

// Disable device interrupt
void dcd_int_disable(uint8_t rhport);

// Receive Set Address request, mcu port must also include status IN response
void dcd_set_address(uint8_t rhport, uint8_t dev_addr);

// Wake up host
void dcd_remote_wakeup(uint8_t rhport);

// Connect by enabling internal pull-up resistor on D+/D-
void dcd_connect(uint8_t rhport);

// Disconnect by disabling internal pull-up resistor on D+/D-
void dcd_disconnect(uint8_t rhport);

// Enable/Disable Start-of-frame interrupt. Default is disabled
void dcd_sof_enable(uint8_t rhport, bool en);

#if CFG_TUD_TEST_MODE
// Put device into a test mode (needs power cycle to quit)
void dcd_enter_test_mode(uint8_t rhport, tusb_feature_test_mode_t test_selector);
#endif
//--------------------------------------------------------------------+
// Endpoint API
//--------------------------------------------------------------------+

// Invoked when a control transfer's status stage is complete.
// May help DCD to prepare for next control transfer, this API is optional.
void dcd_edpt0_status_complete(uint8_t rhport, tusb_control_request_t const * request);

// Configure endpoint's registers according to descriptor
bool dcd_edpt_open            (uint8_t rhport, tusb_desc_endpoint_t const * desc_ep);

// Close all non-control endpoints, cancel all pending transfers if any.
// Invoked when switching from a non-zero Configuration by SET_CONFIGURE therefore
// required for multiple configuration support.
void dcd_edpt_close_all       (uint8_t rhport);

// Submit a transfer, When complete dcd_event_xfer_complete() is invoked to notify the stack
bool dcd_edpt_xfer            (uint8_t rhport, uint8_t ep_addr, uint8_t * buffer, uint16_t total_bytes, bool is_isr);

// Submit an transfer using fifo, When complete dcd_event_xfer_complete() is invoked to notify the stack
// This API is optional, may be useful for register-based for transferring data.
bool dcd_edpt_xfer_fifo       (uint8_t rhport, uint8_t ep_addr, tu_fifo_t * ff, uint16_t total_bytes, bool is_isr);

// Stall endpoint, any queuing transfer should be removed from endpoint
void dcd_edpt_stall           (uint8_t rhport, uint8_t ep_addr);

// clear stall, data toggle is also reset to DATA0
// This API never calls with control endpoints, since it is auto cleared when receiving setup packet
void dcd_edpt_clear_stall     (uint8_t rhport, uint8_t ep_addr);

#ifdef TUP_DCD_EDPT_CLOSE_API
// Close an endpoint.
void dcd_edpt_close(uint8_t rhport, uint8_t ep_addr);

#else

// Allocate packet buffer used by ISO endpoints
// Some MCU need manual packet buffer allocation, we allocate the largest size to avoid clustering
bool dcd_edpt_iso_alloc(uint8_t rhport, uint8_t ep_addr, uint16_t largest_packet_size);

// Configure and enable an ISO endpoint according to descriptor
bool dcd_edpt_iso_activate(uint8_t rhport, tusb_desc_endpoint_t const * desc_ep);

#endif

//--------------------------------------------------------------------+
// Event API (implemented by stack)
//--------------------------------------------------------------------+

// Called by DCD to notify device stack
extern void dcd_event_handler(dcd_event_t const * event, bool in_isr);

// helper to send bus signal event
TU_ATTR_ALWAYS_INLINE static inline void dcd_event_bus_signal (uint8_t rhport, dcd_eventid_t eid, bool in_isr) {
  dcd_event_t event;
  event.rhport = rhport;
  event.event_id = eid;
  dcd_event_handler(&event, in_isr);
}

// helper to send bus reset event
TU_ATTR_ALWAYS_INLINE static inline  void dcd_event_bus_reset (uint8_t rhport, tusb_speed_t speed, bool in_isr) {
  dcd_event_t event;
  event.rhport = rhport;
  event.event_id = DCD_EVENT_BUS_RESET;
  event.bus_reset.speed = speed;
  dcd_event_handler(&event, in_isr);
}

// helper to send setup received
TU_ATTR_ALWAYS_INLINE static inline void dcd_event_setup_received(uint8_t rhport, uint8_t const * setup, bool in_isr) {
  dcd_event_t event;
  event.rhport = rhport;
  event.event_id = DCD_EVENT_SETUP_RECEIVED;
  (void) memcpy(&event.setup_received, setup, sizeof(tusb_control_request_t));
  // USB wire format is little-endian. Convert multi-byte fields to host byte order
  // so the stack always sees correct values regardless of CPU endianness.
  event.setup_received.wValue  = tu_le16toh(event.setup_received.wValue);
  event.setup_received.wIndex  = tu_le16toh(event.setup_received.wIndex);
  event.setup_received.wLength = tu_le16toh(event.setup_received.wLength);
  dcd_event_handler(&event, in_isr);
}

// helper to send transfer complete event
TU_ATTR_ALWAYS_INLINE static inline void dcd_event_xfer_complete (uint8_t rhport, uint8_t ep_addr, uint32_t xferred_bytes, uint8_t result, bool in_isr) {
  dcd_event_t event;
  event.rhport = rhport;
  event.event_id = DCD_EVENT_XFER_COMPLETE;
  event.xfer_complete.ep_addr = ep_addr;
  event.xfer_complete.len     = xferred_bytes;
  event.xfer_complete.result  = result;
  dcd_event_handler(&event, in_isr);
}

TU_ATTR_ALWAYS_INLINE static inline void dcd_event_sof(uint8_t rhport, uint32_t frame_count, bool in_isr) {
  dcd_event_t event;
  event.rhport = rhport;
  event.event_id = DCD_EVENT_SOF;
  event.sof.frame_count = frame_count;
  dcd_event_handler(&event, in_isr);
}

#ifdef __cplusplus
 }
#endif

#endif
