f3l1xa88077/C2S/Software/C2Sv1/Drivers/Custom/tinyusb/board_api.h

/*
 * The MIT License (MIT)
 *
 * Copyright (c) 2019 Ha Thach (tinyusb.org)
 *
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
 * This file is part of the TinyUSB stack.
 */

#ifndef BOARD_API_H_
#define BOARD_API_H_

#ifdef __cplusplus
extern "C" {
#endif

#include <stdint.h>
#include <inttypes.h>
#include <stdbool.h>
#include <string.h>
#include <stdio.h>

#include <tinyusb/tusb.h>
#include "stm32u575xx.h"

#if CFG_TUSB_OS == OPT_OS_ZEPHYR
  #include <zephyr/kernel.h>
#elif CFG_TUSB_OS == OPT_OS_FREERTOS
  #ifdef ESP_PLATFORM
    // ESP-IDF need "freertos/" prefix in include path.
    // CFG_TUSB_OS_INC_PATH should be defined accordingly.
    #include "freertos/FreeRTOS.h"
    #include "freertos/semphr.h"
    #include "freertos/queue.h"
    #include "freertos/task.h"
    #include "freertos/timers.h"
  #else
    #include "FreeRTOS.h"
    #include "semphr.h"
    #include "queue.h"
    #include "task.h"
    #include "timers.h"
  #endif
#endif

// Define the default baudrate
#ifndef CFG_BOARD_UART_BAUDRATE
#define CFG_BOARD_UART_BAUDRATE 115200   ///< Default baud rate
#endif

//--------------------------------------------------------------------+
// Board Porting API
// For simplicity, only one LED and one Button are used
//--------------------------------------------------------------------+

// Initialize on-board peripherals : led, button, uart and USB
void board_init(void);

// Init board after tinyusb is initialized
void board_init_after_tusb(void);

// Jump to bootloader
void board_reset_to_bootloader(void);

// Turn LED on or off
void board_led_write(bool state);

// Control led pattern using phase duration in ms.
// For each phase, LED is toggle then repeated, board_led_task() is required to be called
//void board_led_pattern(uint32_t const phase_ms[], uint8_t count);

// Get the current state of button
// a '1' means active (pressed), a '0' means inactive.
uint32_t board_button_read(void);

// Get board unique ID for USB serial number. Return number of bytes. Note max_len is typically 16
size_t board_get_unique_id(uint8_t id[], size_t max_len);

// Get characters from UART (non-blocking). Return number of read bytes.
int board_uart_read(uint8_t *buf, int len);

// Send characters to UART (non-blocking). Return number of sent bytes
int board_uart_write(void const *buf, int len);

//--------------------------------------------------------------------+
// Helper functions
//--------------------------------------------------------------------+
static inline void board_led_on(void) {
  board_led_write(true);
}

static inline void board_led_off(void) {
  board_led_write(false);
}

size_t board_get_unique_id(uint8_t id[], size_t max_len)
{
  volatile uint8_t *stm32_uid = (volatile uint8_t *) UID_BASE;
  size_t len = (max_len > 12) ? 12 : max_len; // STM32U5 has a 96-bit (12-byte) unique ID

  for (size_t i = 0; i < len; i++)
  {
    id[i] = stm32_uid[i];
  }

  return len;
}

// Get USB Serial number string from unique ID if available. Return number of character.
// Input is string descriptor from index 1 (index 0 is type + len)
static inline size_t board_usb_get_serial(uint16_t desc_str1[], size_t max_chars) {
  uint8_t uid[16] TU_ATTR_ALIGNED(4);
  size_t uid_len;

  // TODO work with make, but not working with esp32s3 cmake
  uid_len = board_get_unique_id(uid, sizeof(uid));

  if ( uid_len > max_chars / 2u ) {
    uid_len = max_chars / 2u;
  }

  for ( size_t i = 0; i < uid_len; i++ ) {
    for ( size_t j = 0; j < 2; j++ ) {
      const unsigned char nibble_to_hex[16] = {
          '0', '1', '2', '3', '4', '5', '6', '7',
          '8', '9', 'A', 'B', 'C', 'D', 'E', 'F'
      };
      const uint8_t nibble = (uint8_t) ((uid[i] >> (j * 4u)) & 0xfu);
      desc_str1[i * 2 + (1 - j)] = nibble_to_hex[nibble]; // UTF-16-LE
    }
  }

  return 2 * uid_len;
}

// TODO remove
static inline void board_delay(uint32_t ms) {
  uint32_t start_ms = tusb_time_millis_api();
  while ( tusb_time_millis_api() - start_ms < ms ) {
    // take chance to run usb background
    #if CFG_TUD_ENABLED
    tud_task();
    #endif

    #if CFG_TUH_ENABLED
    tuh_task();
    #endif
  }
}

// stdio getchar() is blocking, this is non-blocking version
int board_getchar(void);
int board_putchar(int c);

#ifdef __cplusplus
}
#endif

#endif
