f3l1xa88077/C2S/Software/C2Sv1/Core/Inc/app_threadx.h

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

/* Define to prevent recursive inclusion -------------------------------------*/
#ifndef __APP_THREADX_H
#define __APP_THREADX_H
#ifdef __cplusplus
extern "C" {
#endif

/* Includes ------------------------------------------------------------------*/
#include "tx_api.h"

/* USER CODE BEGIN Includes */

#include <stdio.h>
#include <string.h>
#include "ina219.h"
#include "config.h"

// Camera
#include "main.h"
#include "ov7670.h"
#include "linked_list.h"
#include "stm32u5xx_hal_dcmi.h"

// QSPI
#include "AT25xF2561C.h"

// SLEEP/STOP
#include "interrupt.h"
#include "stm32u5xx_hal_tim.h"

/* USER CODE END Includes */

/* Exported types ------------------------------------------------------------*/
/* Exported constants --------------------------------------------------------*/

/* Main thread defines -------------------------------------------------------*/
/* Exported macro ------------------------------------------------------------*/
/* Exported functions prototypes ---------------------------------------------*/
UINT App_ThreadX_Init(VOID *memory_ptr);
void MX_ThreadX_Init(void);

/* USER CODE BEGIN EFP */

void tx_thread_sleep_ms(ULONG ms);

/* USER CODE END EFP */

#ifdef __cplusplus
}
#endif
#endif /* __APP_THREADX_H */
